vkar9898/Cluster2HDMI/KiCad/Cluster2HDMI/Cluster2HDMI.kicad_sch

## KiCad design KiCad/Cluster2HDMI/Cluster2HDMI.kicad_sch (2026-10-10)

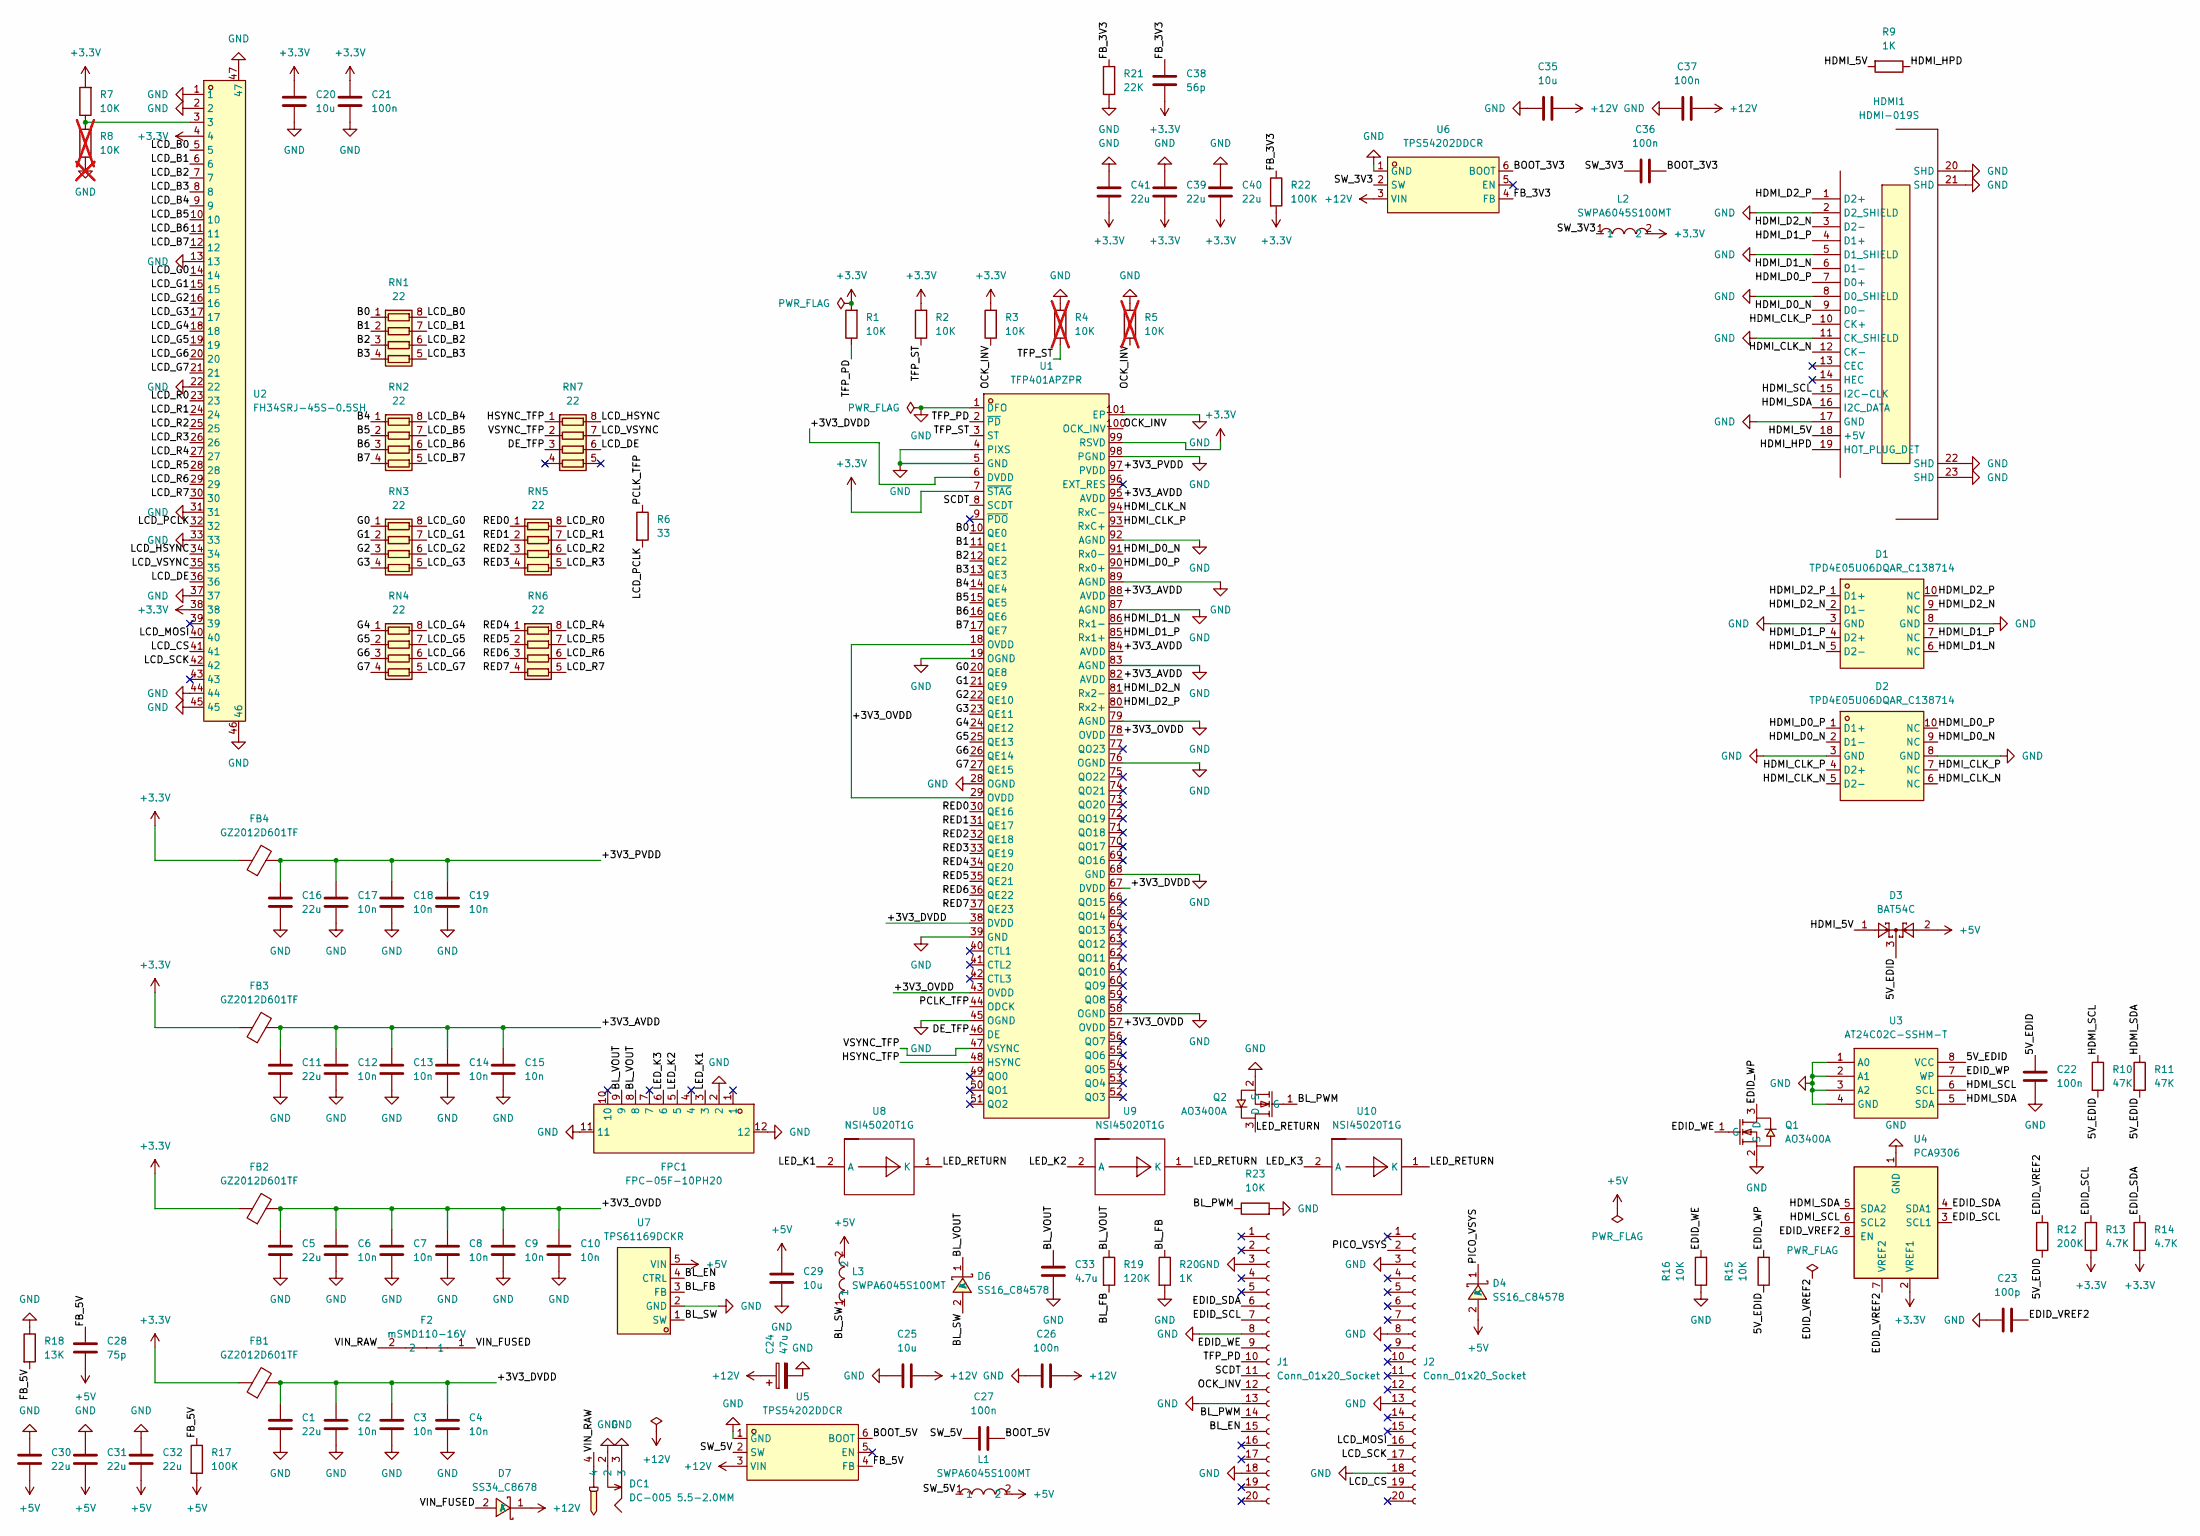
[picture p9: schematic Cluster2HDMI.kicad_sch]

Parts:
C1, C5, C11, C16, C30, C31, C32, C39, C40, C41: 22u; C_0805_2012Metric; LCSC Part C45783
C2, C3, C4, C6, C7, C8, C9, C10, C12, C13, C14, C15, C17, C18, C19: 10n; C_0603_1608Metric; LCSC Part C57112
C20, C25, C29, C35: 10u; C_0805_2012Metric; LCSC Part C15850
C21, C22, C26, C27, C36, C37: 100n; C_0603_1608Metric; LCSC Part C14663
C23: 100p; C_0603_1608Metric; LCSC Part C14858
C24: 47u; CP_Elec_6.3x5.4; LCSC Part C178505
C28: 75p; C_0603_1608Metric; LCSC Part C282074
C33: 4.7u; C_1206_3216Metric; LCSC Part C51205
C38: 56p; C_0603_1608Metric; LCSC Part C39148
D1, D2: TPD4E05U06DQAR_C138714; USON-10_L2.5-W1.0-P0.50-BL; MPN TPD4E05U06DQAR; LCSC Part C138714
D3: BAT54C; SOT-23; LCSC Part C37704
D4, D6: SS16_C84578; SMA_L4.4-W2.6-LS5.0-RD; MPN SS16; LCSC Part C84578
D7: SS34_C8678; SMA_L4.3-W2.6-LS5.2-RD; MPN SS34; LCSC Part C8678
DC1: DC-005 5.5-2.0MM; DC-IN-TH_DC-005-5.5-2.0; MPN DC-005 2.0; LCSC Part C16214
F2: mSMD110-16V; F1812; MPN mSMD110-16V; LCSC Part C69691
FB1, FB2, FB3, FB4: GZ2012D601TF; L_0805_2012Metric; LCSC Part C1017
FPC1: FPC-05F-10PH20; FPC-SMD_10P-P0.50_XUNPU_FPC-05F-10PH20; MPN FPC-05F-10PH20; LCSC Part C2856798
HDMI1: HDMI-019S; HDMI-SMD_HDMI-019S; MPN HDMI-019S; LCSC Part C111617
J1, J2: Conn_01x20_Socket; PinSocket_1x20_P2.54mm_Vertical; LCSC Part C50984
L1, L2, L3: SWPA6045S100MT; IND-SMD_L6.0-W6.0_SWPA6045S; MPN SWPA6045S100MT; LCSC Part C79272
Q1, Q2: AO3400A; SOT-23-3_L2.9-W1.3-P1.90-LS2.4-BR; MPN AO3400A; LCSC Part C20917
R1, R2, R3, R7, R15, R16, R23: 10K; R_0603_1608Metric; LCSC Part C25804
R4, R5, R8: 10K; R_0603_1608Metric; LCSC Part C25804; not fitted
R6: 33; R_0603_1608Metric; LCSC Part C23140
R9, R20: 1K; R_0603_1608Metric; LCSC Part C21190
R10, R11: 47K; R_0603_1608Metric; LCSC Part C25819
R12: 200K; R_0603_1608Metric; LCSC Part C25811
R13, R14: 4.7K; R_0603_1608Metric; LCSC Part C23162
R17, R22: 100K; R_0603_1608Metric; LCSC Part C25803
R18: 13K; R_0603_1608Metric; LCSC Part C22797
R19: 120K; R_0603_1608Metric; LCSC Part C25808
R21: 22K; R_0603_1608Metric; LCSC Part C31850
RN1, RN2, RN3, RN4, RN5, RN6, RN7: 22; R_Array_Convex_4x0603; LCSC Part C12008
U1: TFP401APZPR; HTQFP-100_L14.0-W14.0-P0.50-LS16.0-BL-EP6.2; MPN TFP401APZPR; LCSC Part C962083
U2: FH34SRJ-45S-0.5SH; FPC-SMD_45P-P0.50_FH34SRJ-45S-0.5SH-50; MPN FH34SRJ-45S-0.5SH(50); LCSC Part C3170034
U3: AT24C02C-SSHM-T; SOIC-8_L5.0-W4.0-P1.27-LS6.0-BL; MPN AT24C02C-SSHM-T; LCSC Part C6203
U4: PCA9306; SSOP-8_2.95x2.8mm_P0.65mm; LCSC Part C123752
U5, U6: TPS54202DDCR; SOT-23-6_L2.9-W1.6-P0.95-LS2.8-BL; MPN TPS54202DDCR; LCSC Part C191884
U7: TPS61169DCKR; SC-70-5_L2.1-W1.3-P0.65-LS2.1-BR; MPN TPS61169DCKR; LCSC Part C71045
U8, U9, U10: NSI45020T1G; SOD-123F_L2.8-W1.8-LS3.7-RD; MPN NSI45020T1G; LCSC Part C129159

Connections:
5V_EDID: C22.1, D3.3, R10.2, R11.2, R12.2, R15.1, U3.8 (VCC)
+3.3V: C20.1, C21.1, C38.2, C39.1, C40.1, C41.1, FB1.1, FB2.1, FB3.1, FB4.1, L2.2, R1.2, R2.2, R3.2, R7.2, R13.2, R14.2, R22.2, U1.7 (~STAG), U1.99 (RSVD), U2.4, U2.38, U4.2 (VREF1)
+3V3_AVDD: C11.1, C12.1, C13.1, C14.1, C15.1, FB3.2, U1.82 (AVDD), U1.84 (AVDD), U1.88 (AVDD), U1.95 (AVDD)
+3V3_DVDD: C1.1, C2.1, C3.1, C4.1, FB1.2, U1.6 (DVDD), U1.38 (DVDD), U1.67 (DVDD)
+3V3_OVDD: C5.1, C6.1, C7.1, C8.1, C9.1, C10.1, FB2.2, U1.18 (OVDD), U1.29 (OVDD), U1.43 (OVDD), U1.57 (OVDD), U1.78 (OVDD)
+3V3_PVDD: C16.1, C17.1, C18.1, C19.1, FB4.2, U1.97 (PVDD)
+5V: C28.2, C29.1, C30.1, C31.1, C32.1, D3.2, D4.2 (A), L1.2, L3.2, R17.2, U7.5 (VIN)
+12V: C24.1, C25.2, C26.2, C35.2, C37.2, D7.1 (K), U5.3 (VIN), U6.3 (VIN)
B0: RN1.1 (R1.1), U1.10 (QE0)
B1: RN1.2 (R2.1), U1.11 (QE1)
B2: RN1.3 (R3.1), U1.12 (QE2)
B3: RN1.4 (R4.1), U1.13 (QE3)
B4: RN2.1 (R1.1), U1.14 (QE4)
B5: RN2.2 (R2.1), U1.15 (QE5)
B6: RN2.3 (R3.1), U1.16 (QE6)
B7: RN2.4 (R4.1), U1.17 (QE7)
BL_EN: J1.15, U7.4 (CTRL)
BL_FB: R19.2, R20.1, U7.3 (FB)
BL_PWM: J1.14, Q2.1 (G), R23.1
BL_SW: D6.2 (A), L3.1, U7.1 (SW)
BL_VOUT: C33.1, D6.1 (K), FPC1.8, FPC1.9, R19.1
BOOT_3V3: C36.2, U6.6 (BOOT)
BOOT_5V: C27.2, U5.6 (BOOT)
DE_TFP: RN7.3 (R3.1), U1.46 (DE)
EDID_SCL: J1.7, R13.1, U4.3 (SCL1)
EDID_SDA: J1.6, R14.1, U4.4 (SDA1)
EDID_VREF2: C23.2, R12.1, U4.7 (VREF2), U4.8 (EN)
EDID_WE: J1.9, Q1.1 (G), R16.2
EDID_WP: Q1.3 (D), R15.2, U3.7 (WP)
FB_3V3: C38.1, R21.2, R22.1, U6.4 (FB)
FB_5V: C28.1, R17.1, R18.2, U5.4 (FB)
G0: RN3.1 (R1.1), U1.20 (QE8)
G1: RN3.2 (R2.1), U1.21 (QE9)
G2: RN3.3 (R3.1), U1.22 (QE10)
G3: RN3.4 (R4.1), U1.23 (QE11)
G4: RN4.1 (R1.1), U1.24 (QE12)
G5: RN4.2 (R2.1), U1.25 (QE13)
G6: RN4.3 (R3.1), U1.26 (QE14)
G7: RN4.4 (R4.1), U1.27 (QE15)
GND: C1.2, C2.2, C3.2, C4.2, C5.2, C6.2, C7.2, C8.2, C9.2, C10.2, C11.2, C12.2, C13.2, C14.2, C15.2, C16.2, C17.2, C18.2, C19.2, C20.2, C21.2, C22.2, C23.1, C24.2, C25.1, C26.1, C29.2, C30.2, C31.2, C32.2, C33.2, C35.1, C37.1, C39.2, C40.2, C41.2, D1.3 (GND), D1.8 (GND), D2.3 (GND), D2.8 (GND), DC1.2, DC1.3, FPC1.2, FPC1.11, FPC1.12, HDMI1.2 (D2_SHIELD), HDMI1.5 (D1_SHIELD), HDMI1.8 (D0_SHIELD), HDMI1.11 (CK_SHIELD), HDMI1.17 (GND), HDMI1.20 (SHD), HDMI1.21 (SHD), HDMI1.22 (SHD), HDMI1.23 (SHD), J1.3, J1.8, J1.13, J1.18, J2.3, J2.8, J2.13, J2.18, Q1.2 (S), Q2.2 (S), R4.2, R5.2, R8.1, R16.1, R18.1, R20.2, R21.1, R23.2, U1.1 (DFO), U1.4 (PIXS), U1.5 (GND), U1.19 (OGND), U1.28 (OGND), U1.39 (GND), U1.45 (OGND), U1.58 (OGND), U1.68 (GND), U1.76 (OGND), U1.79 (AGND), U1.83 (AGND), U1.87 (AGND), U1.89 (AGND), U1.92 (AGND), U1.98 (PGND), U1.101 (EP), U2.1, U2.2, U2.13, U2.22, U2.31, U2.33, U2.37, U2.44, U2.45, U2.46, U2.47, U3.1 (A0), U3.2 (A1), U3.3 (A2), U3.4 (GND), U4.1 (GND), U5.1 (GND), U6.1 (GND), U7.2 (GND)
HDMI_5V: D3.1, HDMI1.18 (+5V), R9.2
HDMI_CLK_N: D2.5 (D2-), D2.6 (NC), HDMI1.12 (CK-), U1.94 (RxC−)
HDMI_CLK_P: D2.4 (D2+), D2.7 (NC), HDMI1.10 (CK+), U1.93 (RxC+)
HDMI_D0_N: D2.2 (D1-), D2.9 (NC), HDMI1.9 (D0-), U1.91 (Rx0−)
HDMI_D0_P: D2.1 (D1+), D2.10 (NC), HDMI1.7 (D0+), U1.90 (Rx0+)
HDMI_D1_N: D1.5 (D2-), D1.6 (NC), HDMI1.6 (D1-), U1.86 (Rx1−)
HDMI_D1_P: D1.4 (D2+), D1.7 (NC), HDMI1.4 (D1+), U1.85 (Rx1+)
HDMI_D2_N: D1.2 (D1-), D1.9 (NC), HDMI1.3 (D2-), U1.81 (Rx2−)
HDMI_D2_P: D1.1 (D1+), D1.10 (NC), HDMI1.1 (D2+), U1.80 (Rx2+)
HDMI_HPD: HDMI1.19 (HOT_PLUG_DET), R9.1
HDMI_SCL: HDMI1.15 (I2C-CLK), R10.1, U3.6 (SCL), U4.6 (SCL2)
HDMI_SDA: HDMI1.16 (I2C_DATA), R11.1, U3.5 (SDA), U4.5 (SDA2)
HSYNC_TFP: RN7.1 (R1.1), U1.48 (HSYNC)
LCD_B0: RN1.8 (R1.2), U2.5
LCD_B1: RN1.7 (R2.2), U2.6
LCD_B2: RN1.6 (R3.2), U2.7
LCD_B3: RN1.5 (R4.2), U2.8
LCD_B4: RN2.8 (R1.2), U2.9
LCD_B5: RN2.7 (R2.2), U2.10
LCD_B6: RN2.6 (R3.2), U2.11
LCD_B7: RN2.5 (R4.2), U2.12
LCD_CS: J2.19, U2.41
LCD_DE: RN7.6 (R3.2), U2.36
LCD_G0: RN3.8 (R1.2), U2.14
LCD_G1: RN3.7 (R2.2), U2.15
LCD_G2: RN3.6 (R3.2), U2.16
LCD_G3: RN3.5 (R4.2), U2.17
LCD_G4: RN4.8 (R1.2), U2.18
LCD_G5: RN4.7 (R2.2), U2.19
LCD_G6: RN4.6 (R3.2), U2.20
LCD_G7: RN4.5 (R4.2), U2.21
LCD_HSYNC: RN7.8 (R1.2), U2.34
LCD_MOSI: J2.16, U2.40
LCD_PCLK: R6.2, U2.32
LCD_R0: RN5.8 (R1.2), U2.23
LCD_R1: RN5.7 (R2.2), U2.24
LCD_R2: RN5.6 (R3.2), U2.25
LCD_R3: RN5.5 (R4.2), U2.26
LCD_R4: RN6.8 (R1.2), U2.27
LCD_R5: RN6.7 (R2.2), U2.28
LCD_R6: RN6.6 (R3.2), U2.29
LCD_R7: RN6.5 (R4.2), U2.30
LCD_SCK: J2.17, U2.42
LCD_VSYNC: RN7.7 (R2.2), U2.35
LED_K1: FPC1.3, U8.2 (A)
LED_K2: FPC1.5, U9.2 (A)
LED_K3: FPC1.6, U10.2 (A)
LED_RETURN: Q2.3 (D), U8.1 (K), U9.1 (K), U10.1 (K)
unnamed: R7.1, R8.2, U2.3
OCK_INV: J1.12, R3.1, R5.1, U1.100 (OCK_INV)
PCLK_TFP: R6.1, U1.44 (ODCK)
PICO_VSYS: D4.1 (K), J2.2
RED0: RN5.1 (R1.1), U1.30 (QE16)
RED1: RN5.2 (R2.1), U1.31 (QE17)
RED2: RN5.3 (R3.1), U1.32 (QE18)
RED3: RN5.4 (R4.1), U1.33 (QE19)
RED4: RN6.1 (R1.1), U1.34 (QE20)
RED5: RN6.2 (R2.1), U1.35 (QE21)
RED6: RN6.3 (R3.1), U1.36 (QE22)
RED7: RN6.4 (R4.1), U1.37 (QE23)
SCDT: J1.11, U1.8 (SCDT)
SW_3V3: C36.1, L2.1, U6.2 (SW)
SW_5V: C27.1, L1.1, U5.2 (SW)
TFP_PD: J1.10, R1.1, U1.2 (~PD)
TFP_ST: R2.1, R4.1, U1.3 (ST)
VIN_FUSED: D7.2 (A), F2.1
VIN_RAW: DC1.4, F2.2
VSYNC_TFP: RN7.2 (R2.1), U1.47 (VSYNC)
